jacek13/Snake-game-AVR-ATmega328P/resources/photos/20220108_112406.jpg

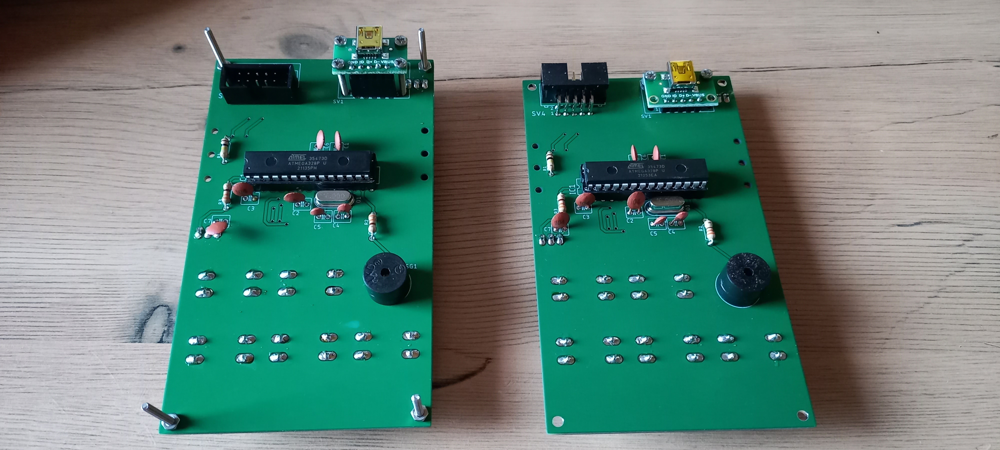
resources/photos/20220108_112406.jpg
